xingyaodad/HeadNeckControl/images/circuit_reference.jpg

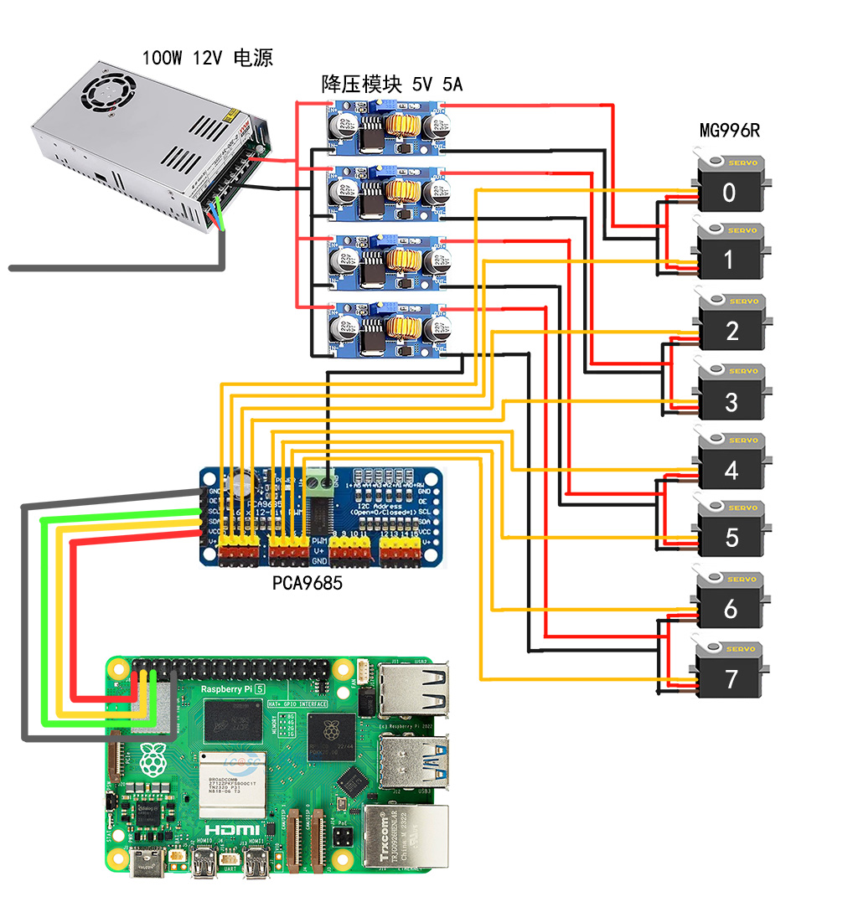
images/circuit_reference.jpg
