xingyaodad/HeadNeckControl/images/dyneema绳 直径1.5mm 5米.jpg

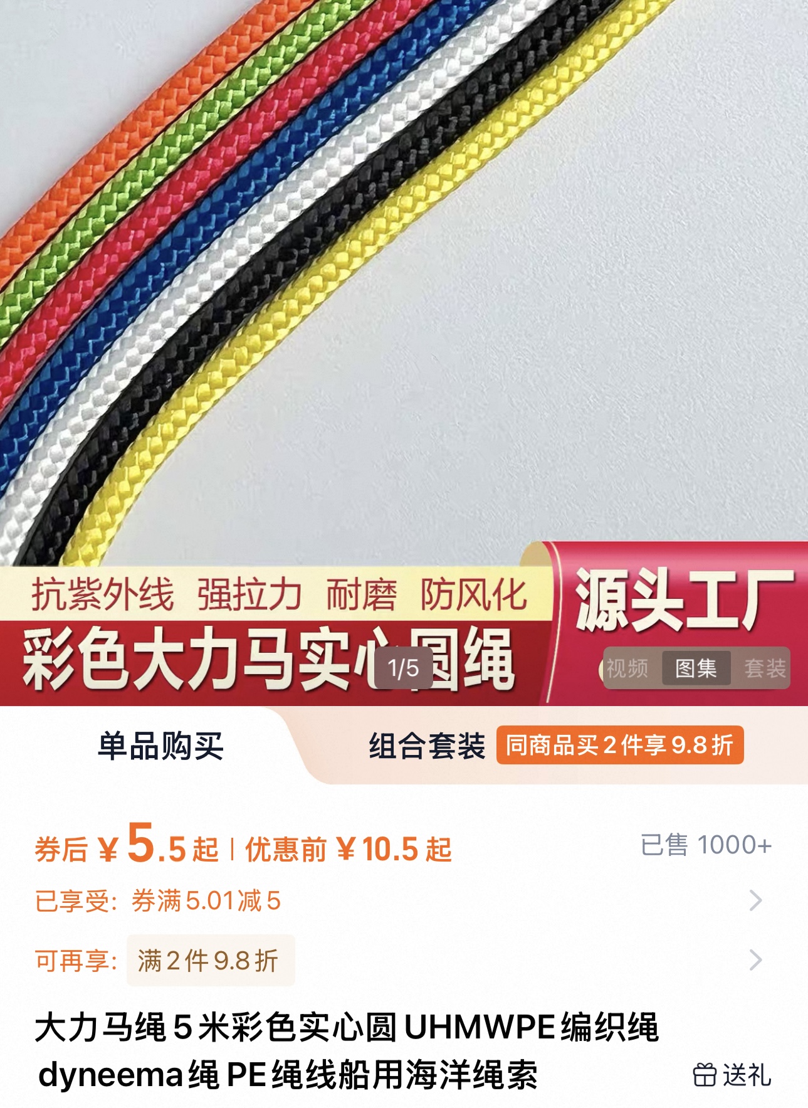
images/dyneema绳 直径1.5mm 5米.jpg
