xingyaodad/HeadNeckControl/images/lengthofthepipe.jpg

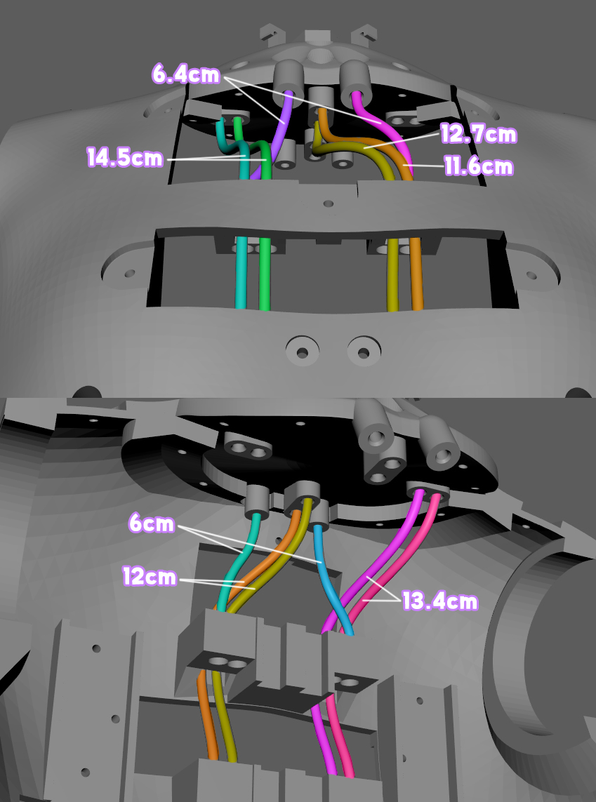
images/lengthofthepipe.jpg
