xingyaodad/HeadNeckControl/images/servo_line.jpg

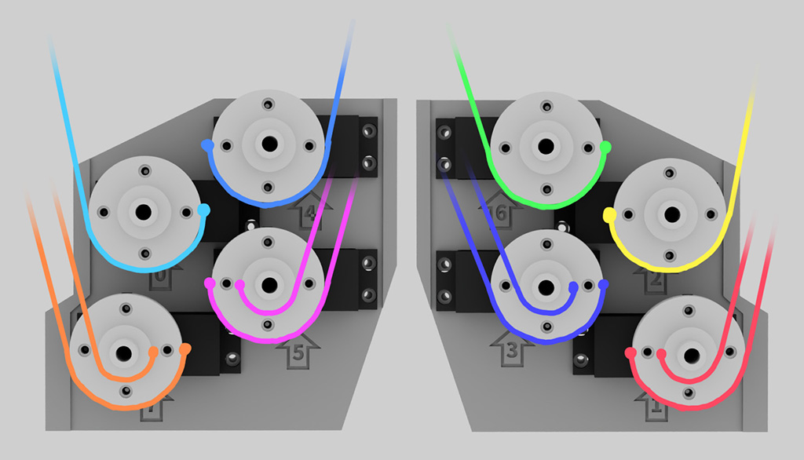
images/servo_line.jpg
