xingyaodad/HeadNeckControl/images/TPU胶圈.jpg

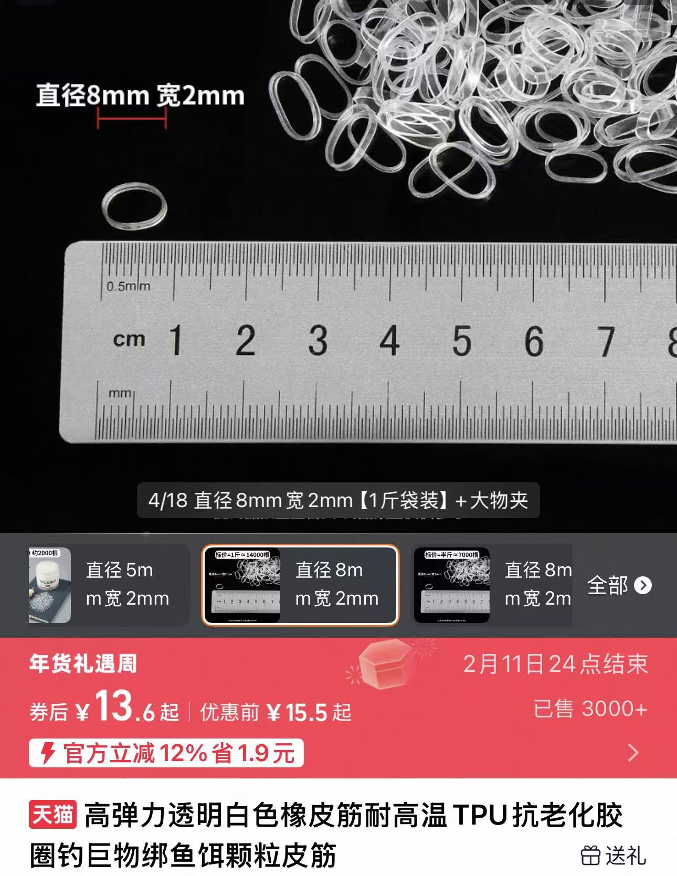
images/TPU胶圈.jpg
