xingyaodad/HeadNeckControl/images/搜陶瓷眼或AMS进料口保护器（小外径3.9  孔2.3  总高6）.jpg

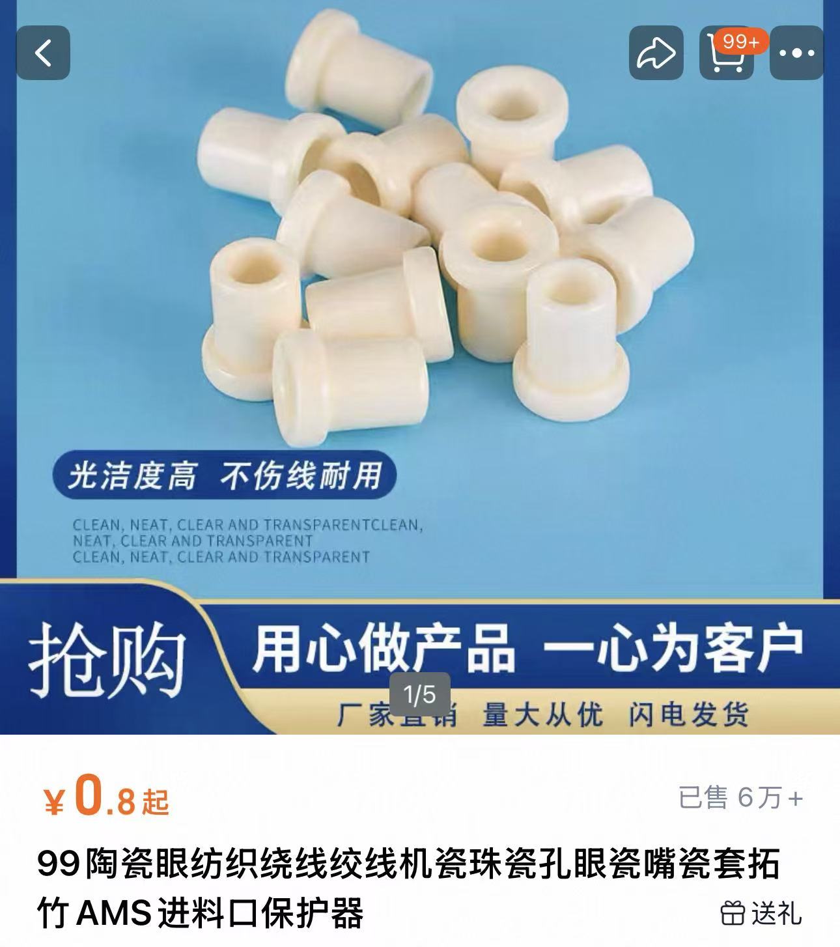
images/搜陶瓷眼或AMS进料口保护器（小外径3.9 孔2.3 总高6）.jpg
