xingyaodad/HeadNeckControl/images/特氟龙硬管 内径2mm  外径3mm 2米.jpg

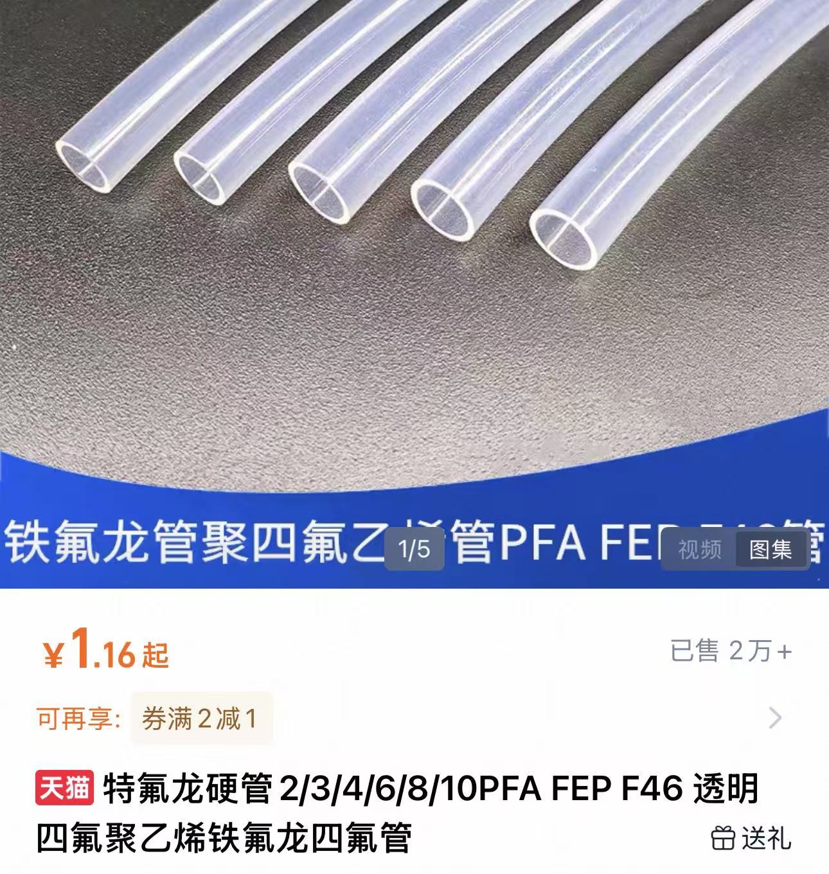
images/特氟龙硬管 内径2mm 外径3mm 2米.jpg
