xingyaodad/HeadNeckControl/images/角度参考/角度参考.jpg

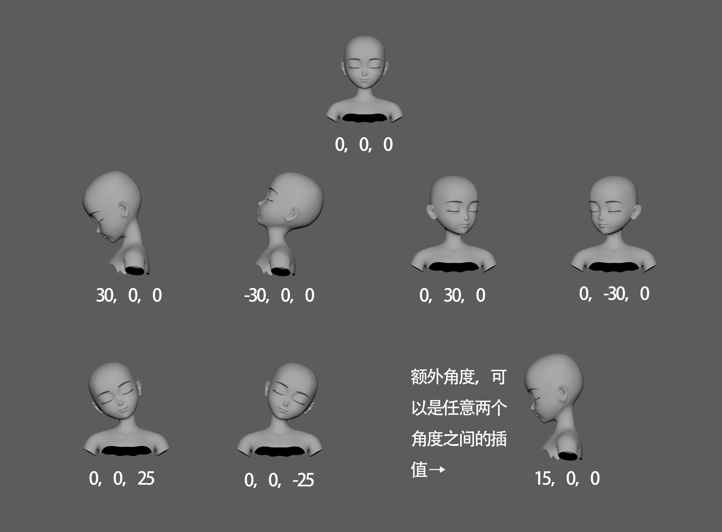
images/角度参考/角度参考.jpg
