xingyaodad/HeadNeckControl/3D-Models/拉线机构.3mf

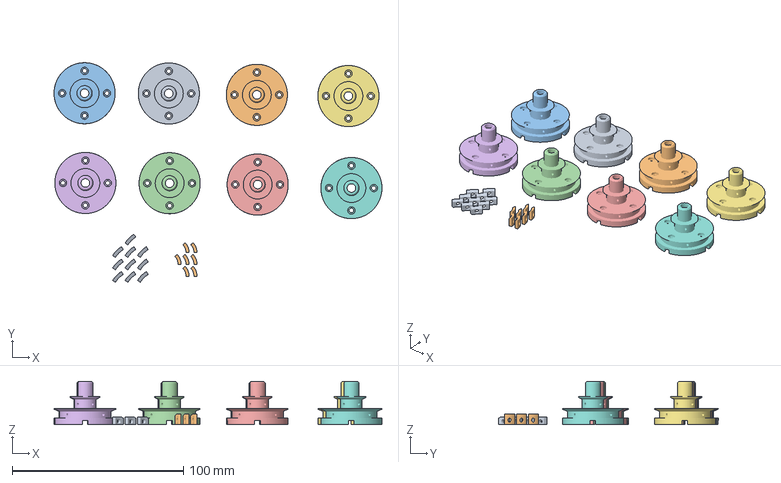
[picture p58: CAD file, 2026-01-31]
3D-Models/拉线机构.3mf
191.8 x 128.4 x 25.2 mm
cable_guide.obj x 8
组合体 x 2
