xingyaodad/HeadNeckControl/3D-Models/neck_support3.obj

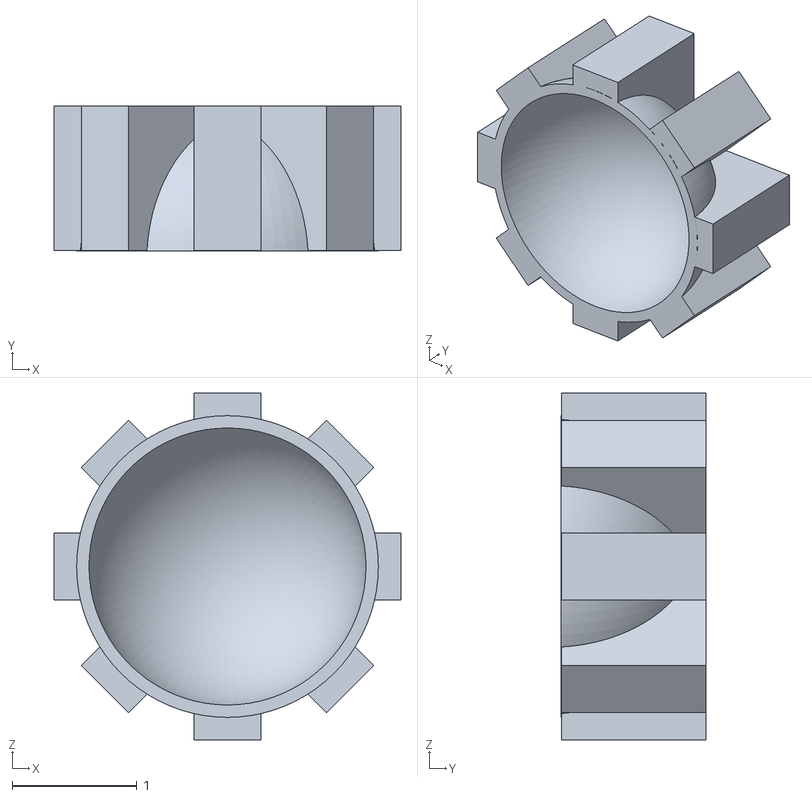
[picture p59: CAD file, 2026-01-31]
3D-Models/neck_support3.obj
2.78 x 1.16 x 2.78
