xingyaodad/HeadNeckControl/3D-Models/chest_block1.obj

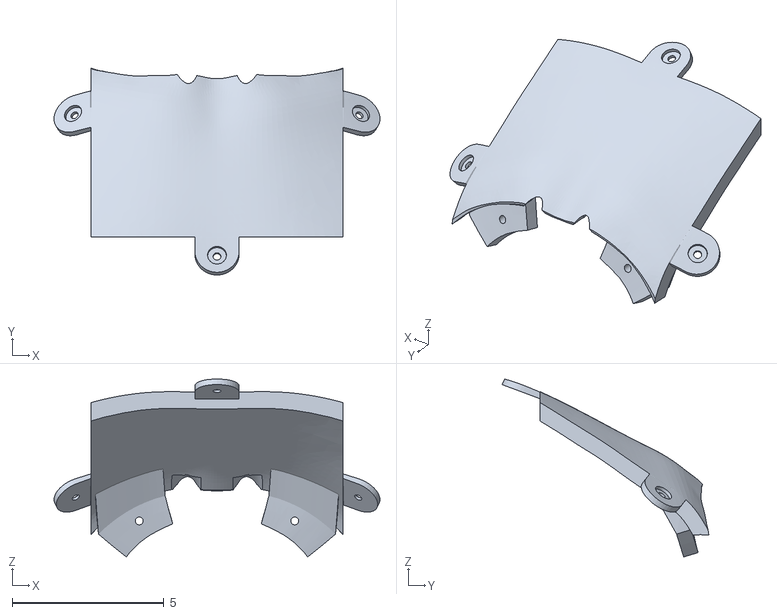
[picture p60: CAD file, 2026-01-31]
3D-Models/chest_block1.obj
10.8 x 6.83 x 5.87
