xingyaodad/HeadNeckControl/3D-Models/platform.obj

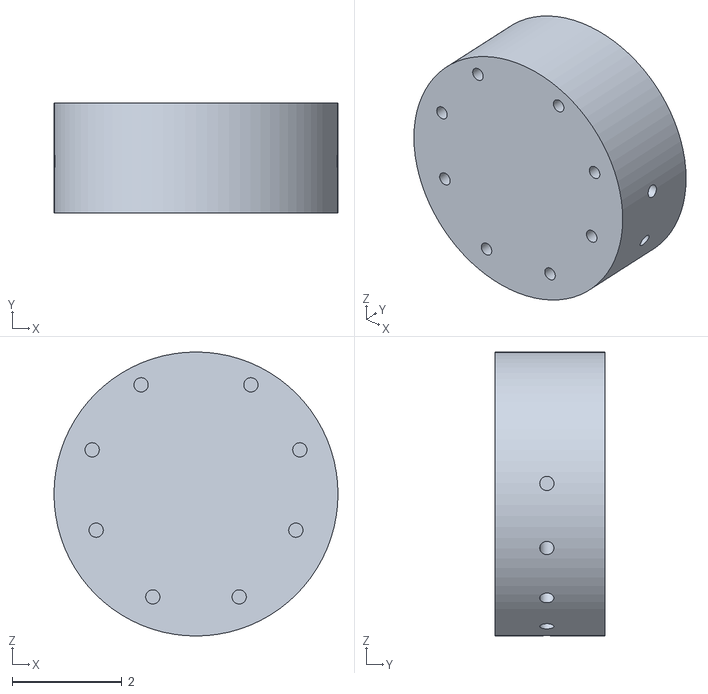
[picture p61: CAD file, 2026-01-31]
3D-Models/platform.obj
5.18 x 2.01 x 5.18
