xingyaodad/HeadNeckControl/3D-Models/cable_guide.obj

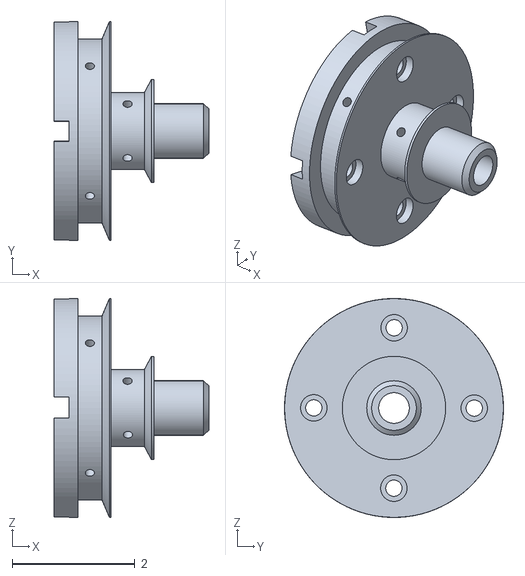
[picture p62: CAD file, 2026-01-31]
3D-Models/cable_guide.obj
2.52 x 3.58 x 3.58
