xingyaodad/HeadNeckControl/3D-Models/back_block1.obj

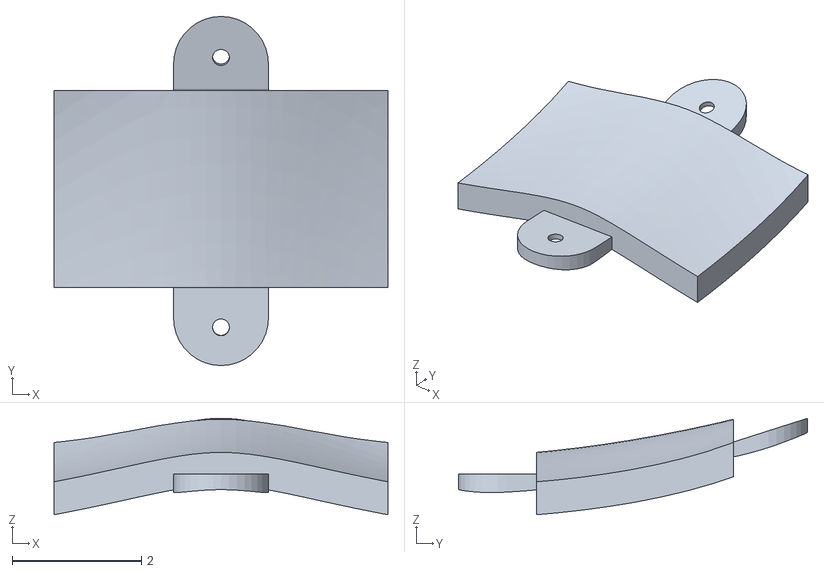
[picture p63: CAD file, 2026-01-31]
3D-Models/back_block1.obj
5.17 x 5.40 x 1.49
