xingyaodad/HeadNeckControl/3D-Models/neck_support2.obj

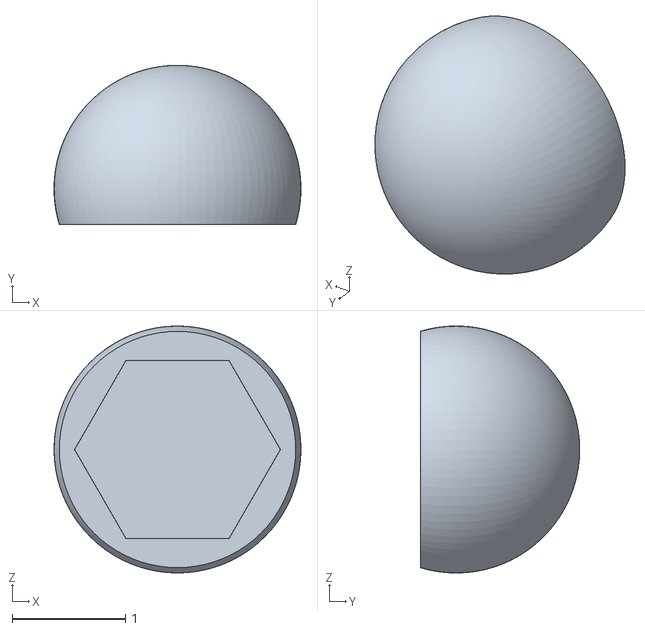
[picture p64: CAD file, 2026-01-31]
3D-Models/neck_support2.obj
2.18 x 1.41 x 2.18
