xingyaodad/HeadNeckControl/3D-Models/neck3.obj

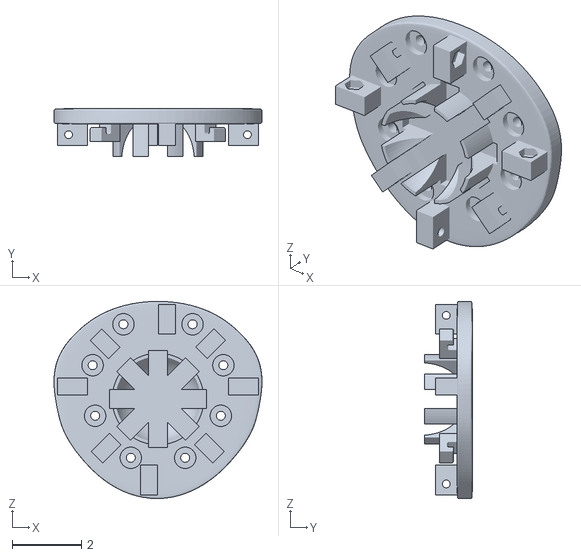
[picture p65: CAD file, 2026-01-31]
3D-Models/neck3.obj
6.02 x 1.38 x 5.71
