xingyaodad/HeadNeckControl/3D-Models/fixed_block_right.obj

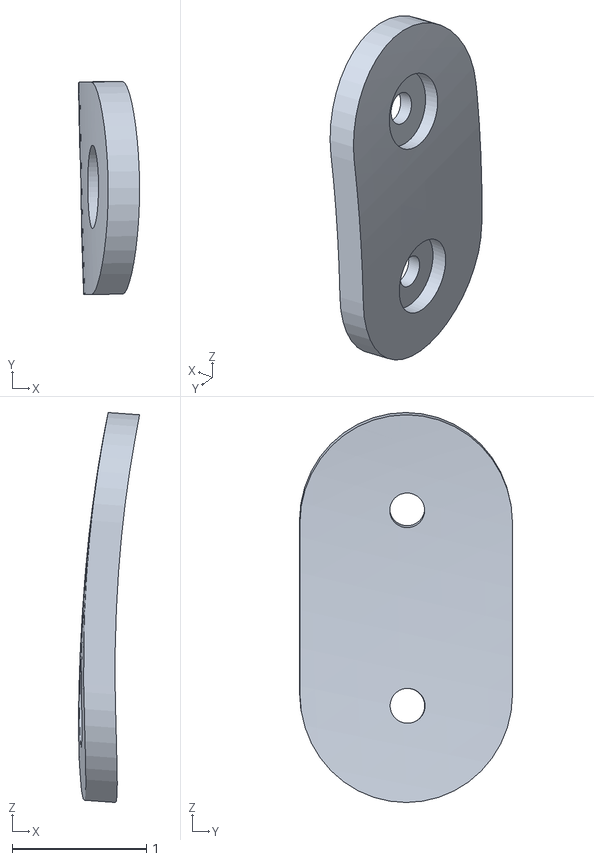
[picture p66: CAD file, 2026-01-31]
3D-Models/fixed_block_right.obj
0.455 x 1.59 x 2.91
