xingyaodad/HeadNeckControl/3D-Models/neck2.obj

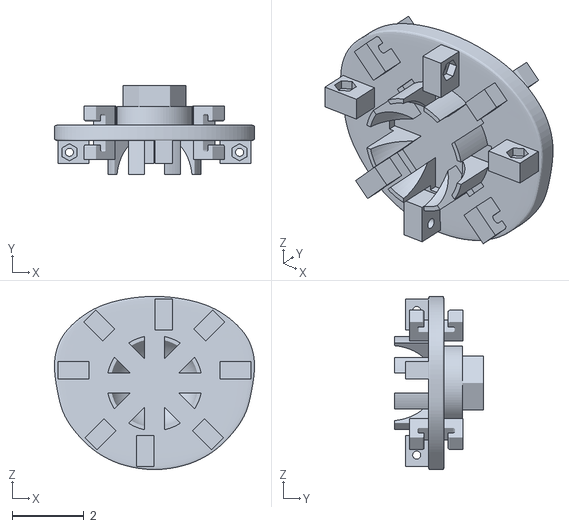
[picture p67: CAD file, 2026-01-31]
3D-Models/neck2.obj
5.57 x 2.47 x 4.82
