xingyaodad/HeadNeckControl/3D-Models/cable_clamp_x8.obj

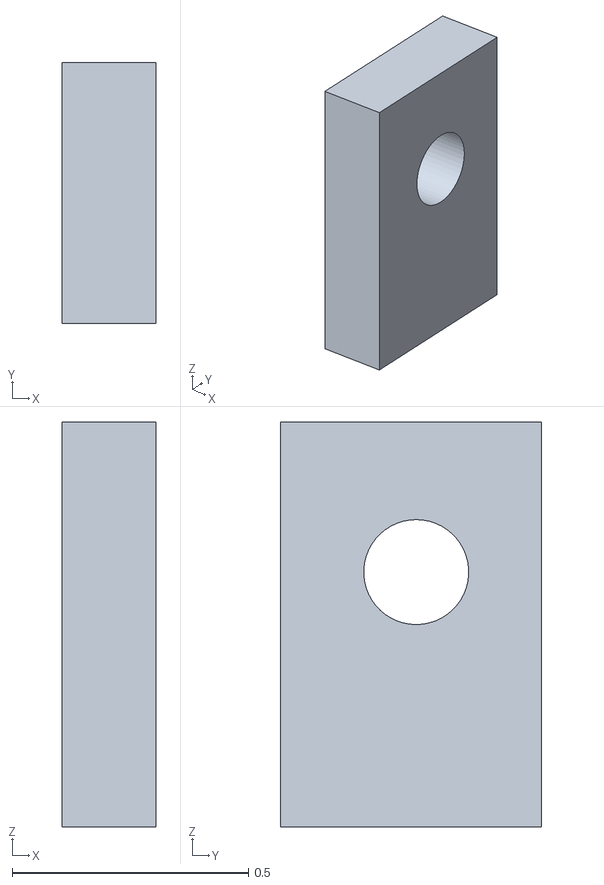
[picture p68: CAD file, 2026-01-31]
3D-Models/cable_clamp_x8.obj
0.199 x 0.552 x 0.857
