xingyaodad/HeadNeckControl/3D-Models/insert_panel_left.obj

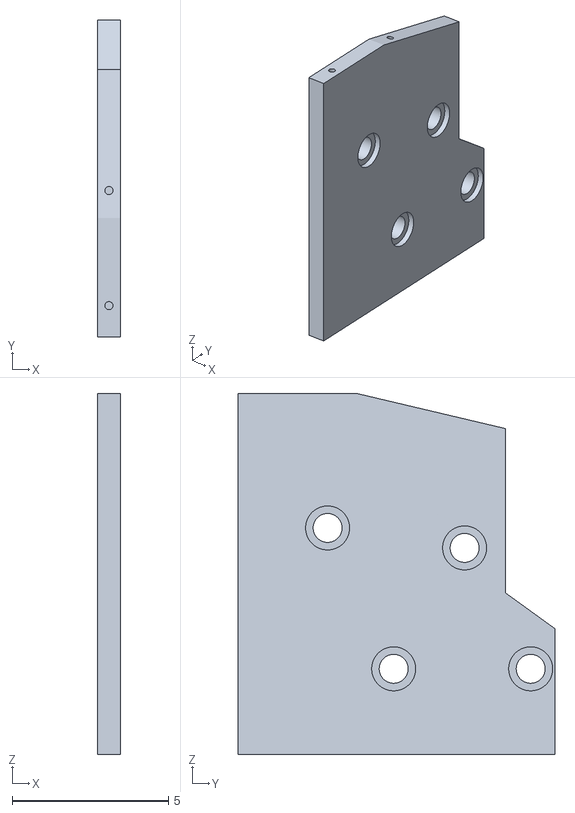
[picture p69: CAD file, 2026-01-31]
3D-Models/insert_panel_left.obj
0.736 x 10.1 x 11.5
