xingyaodad/HeadNeckControl/3D-Models/upper_fixed_block_left.obj

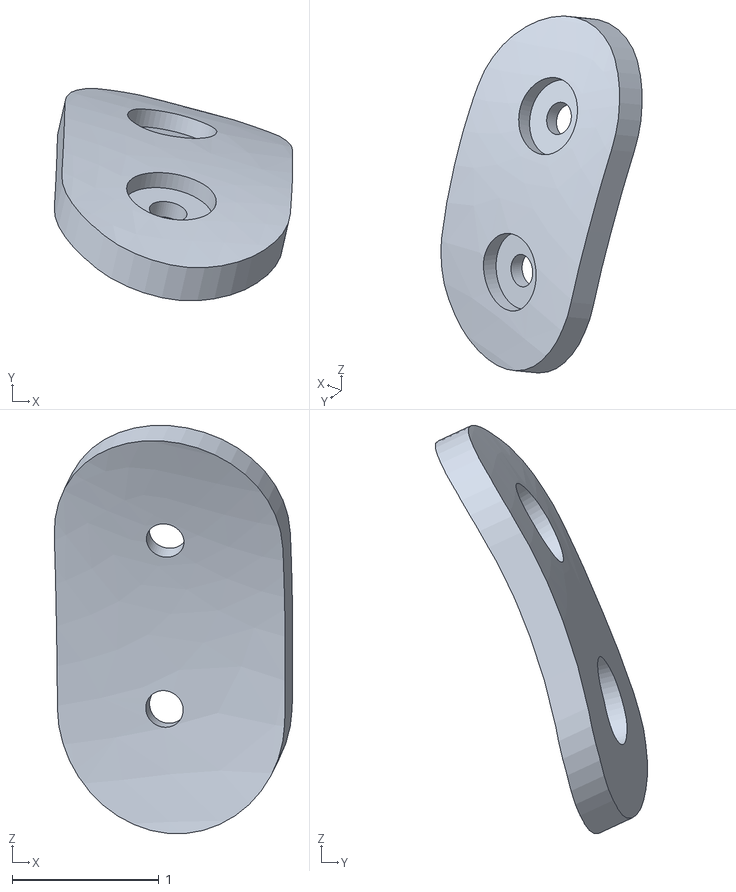
[picture p70: CAD file, 2026-01-31]
3D-Models/upper_fixed_block_left.obj
1.63 x 1.45 x 2.78
