xingyaodad/HeadNeckControl/3D-Models/脖子中间支撑_PA.3mf

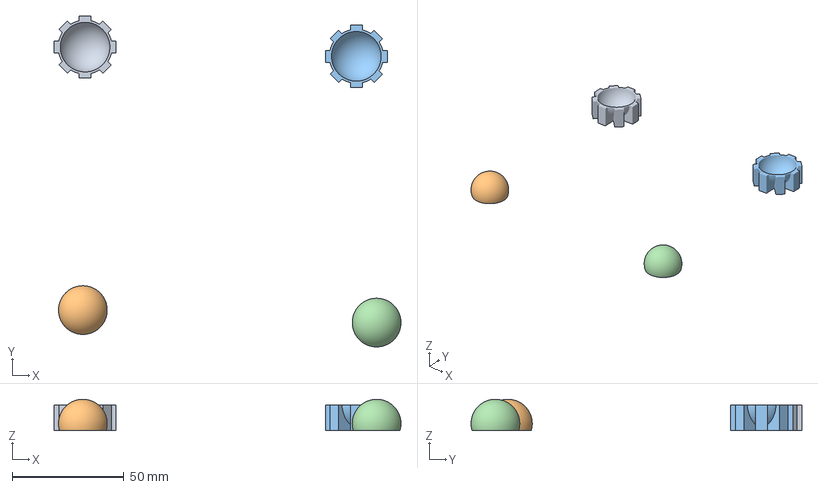
[picture p71: CAD file, 2026-01-31]
3D-Models/脖子中间支撑_PA.3mf
155.3 x 148.1 x 14.1 mm
neck_support1.obj
neck_support2.obj
neck_support3.obj
neck_support4.obj
